NothingCooker/glowby_starlight/pic/IMG20260314133844.jpg

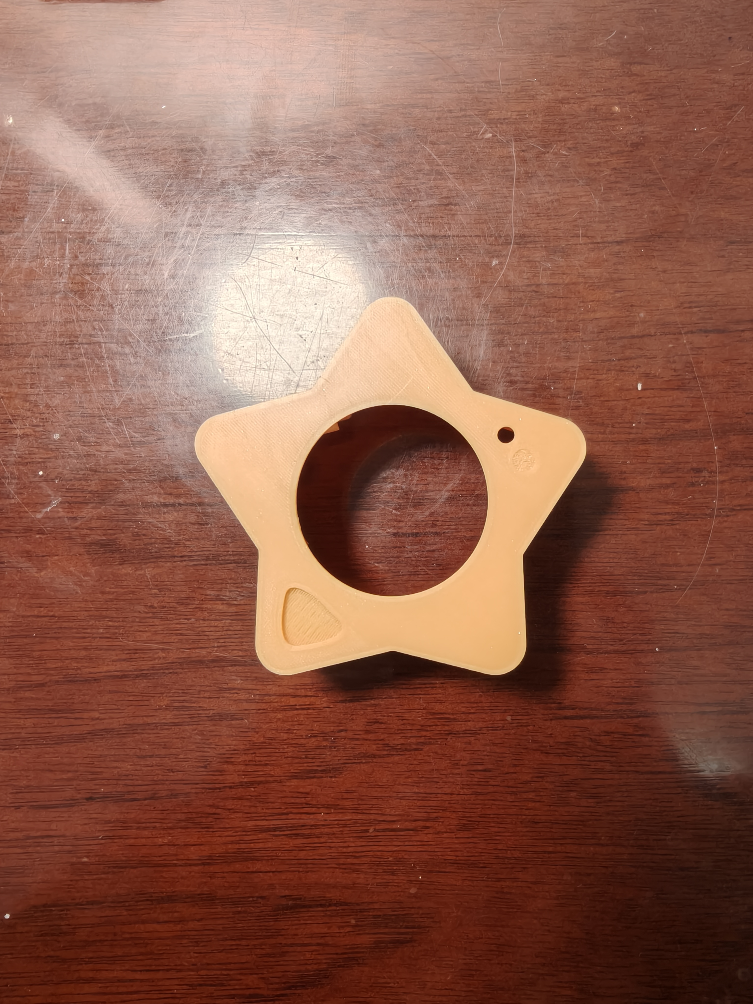
pic/IMG20260314133844.jpg
