NothingCooker/glowby_starlight/starui/1cool.png

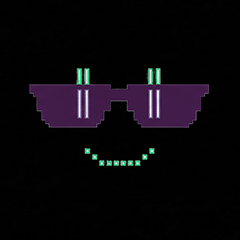
starui/1cool.png
