NothingCooker/glowby_starlight/starui/1happy.png

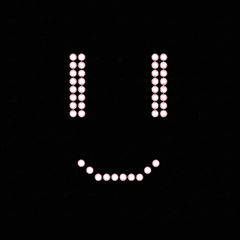
starui/1happy.png
