NothingCooker/glowby_starlight/starui/1superhappy.png

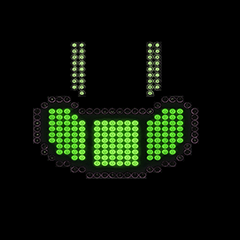
starui/1superhappy.png
