NothingCooker/glowby_starlight/starui/1worried.png

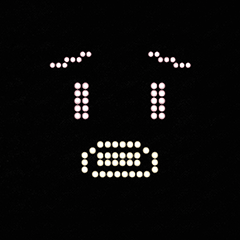
starui/1worried.png
