NothingCooker/glowby_starlight/starui/2afraid.png

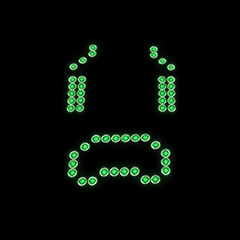
starui/2afraid.png
